EnAccess/OpenSmartMeter/hardware/design_images/3D PCB back.png

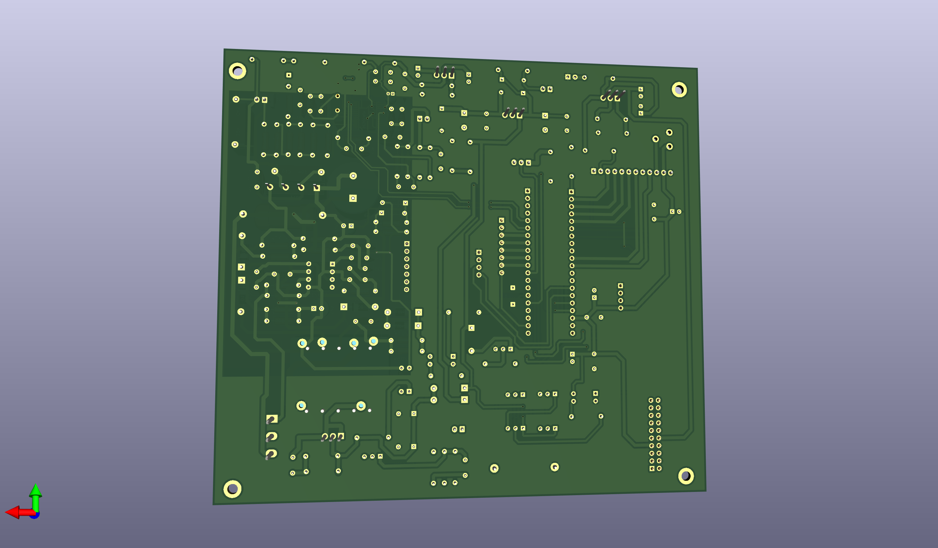
hardware/design_images/3D PCB back.png
