EnAccess/OpenSmartMeter/hardware/design_images/3D PCB front.png

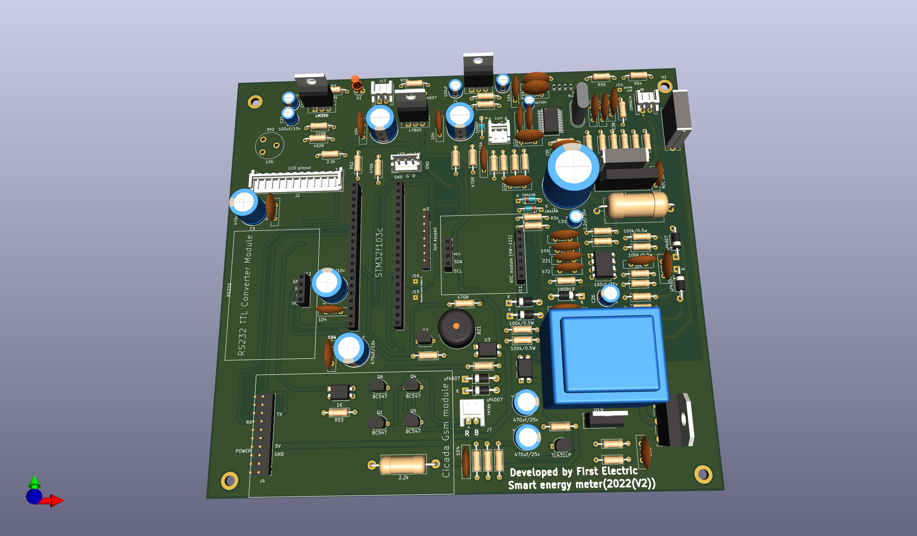
hardware/design_images/3D PCB front.png
