EnAccess/OpenSmartMeter/hardware/design_images/3D PCB right side view.png

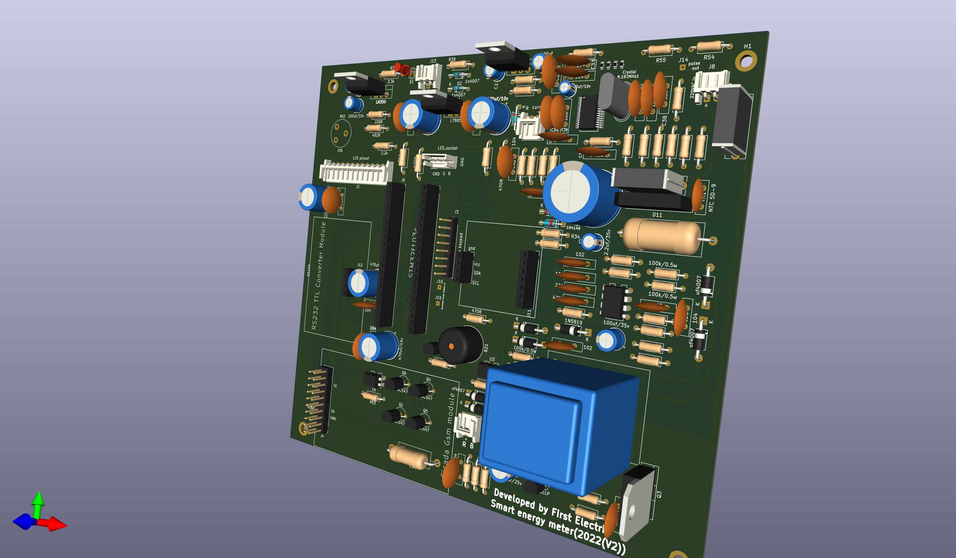
hardware/design_images/3D PCB right side view.png
