EnAccess/OpenSmartMeter/hardware/design_images/first meter prototype.JPG

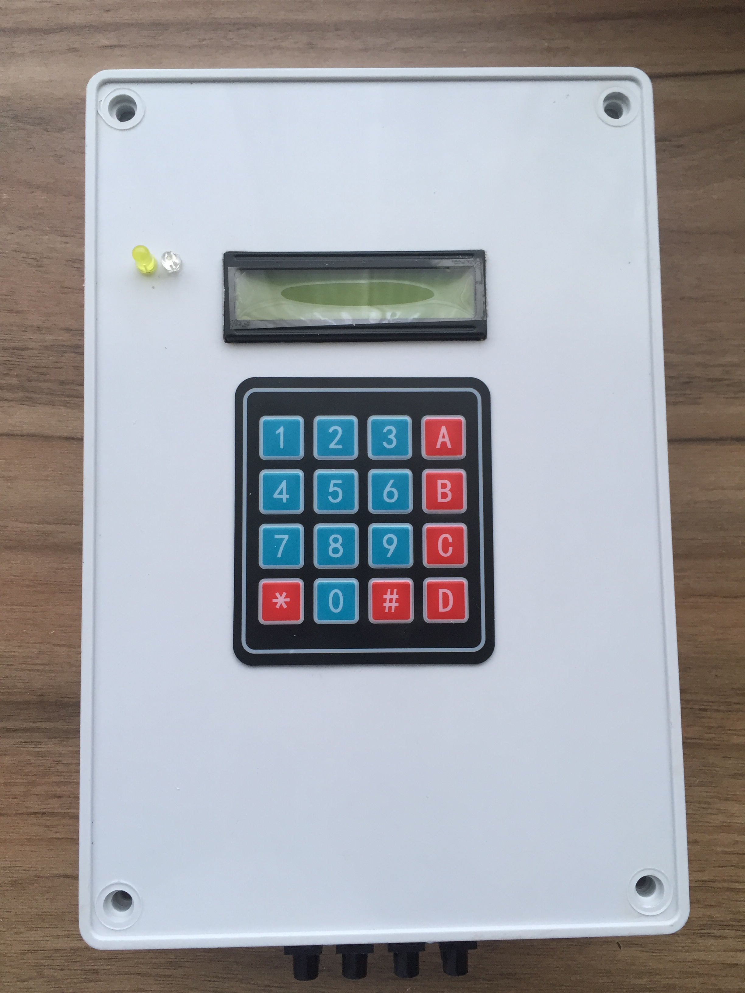
hardware/design_images/first meter prototype.JPG
