EnAccess/OpenSmartMeter/hardware/design_images/meter25 terminal block view.JPG

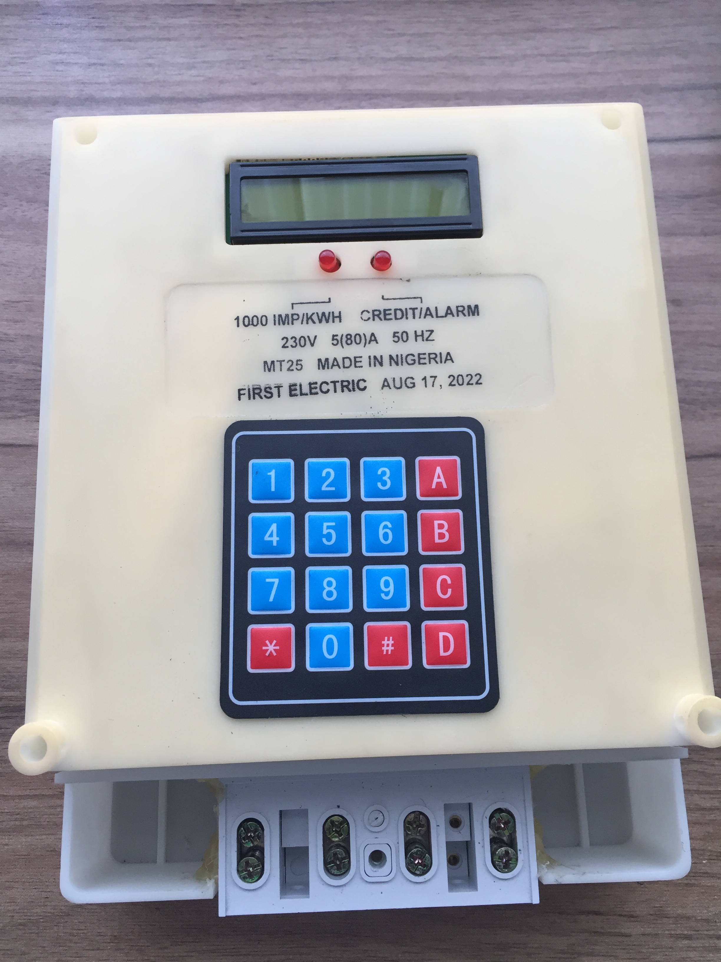
hardware/design_images/meter25 terminal block view.JPG
