EnAccess/OpenSmartMeter/hardware/design_images/meter50 terminal block view.JPG

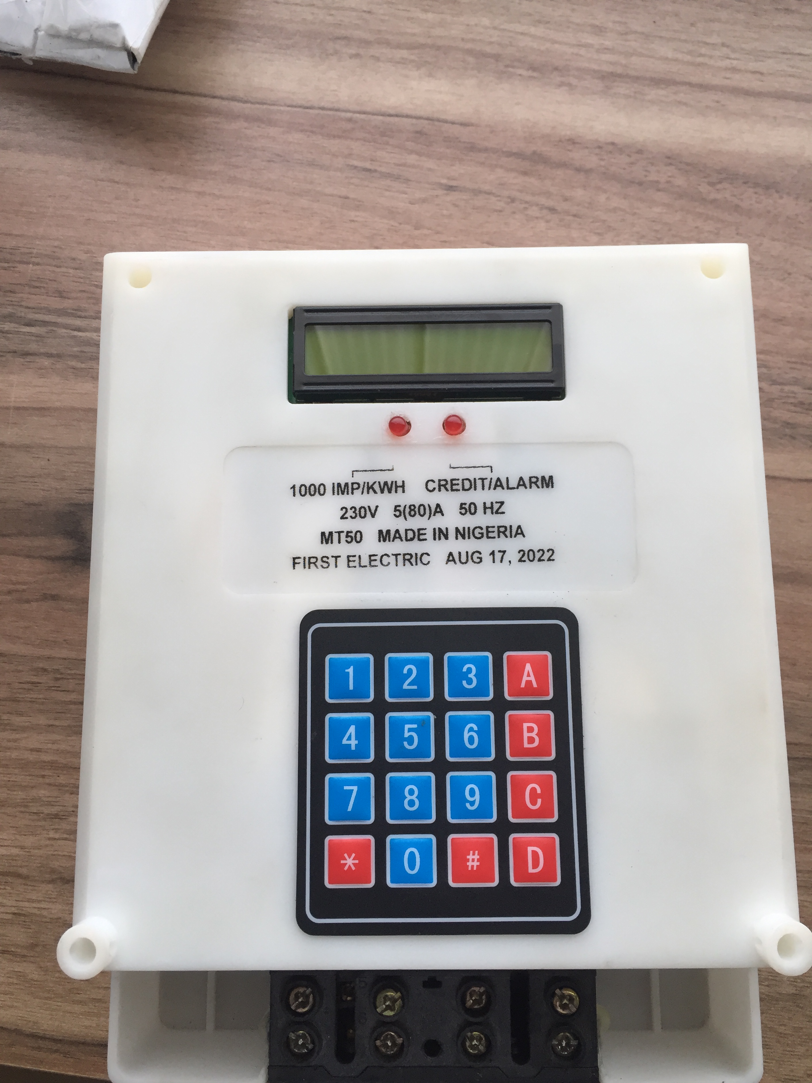
hardware/design_images/meter50 terminal block view.JPG
