EnAccess/OpenSmartMeter/hardware/design_images/meter100.JPG

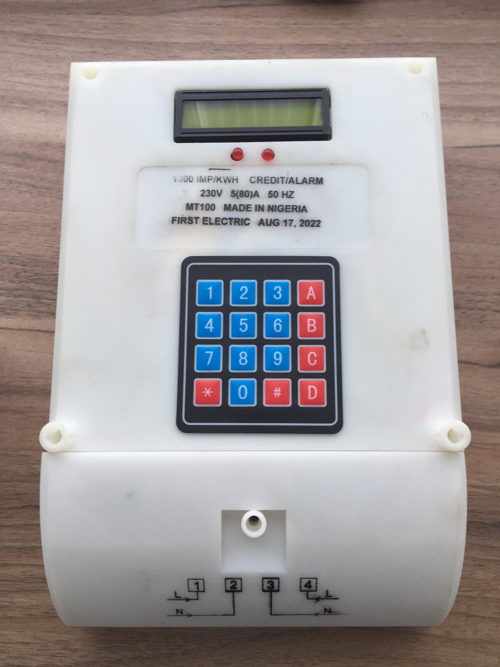
hardware/design_images/meter100.JPG
