EnAccess/OpenSmartMeter/hardware/exterior_casing_design/meter bottom view.png

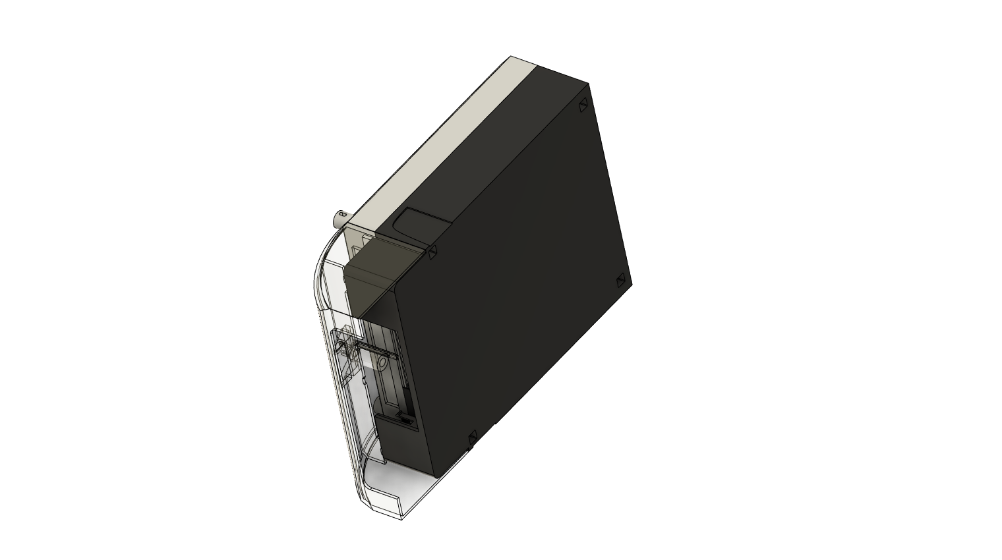
hardware/exterior_casing_design/meter bottom view.png
