EnAccess/OpenSmartMeter/web_software/assets/img/abt.jpg

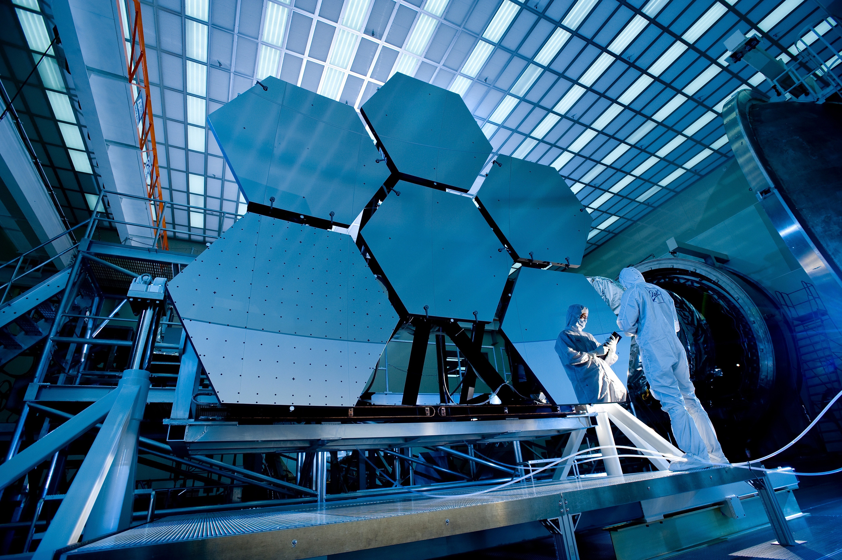
web_software/assets/img/abt.jpg
