EnAccess/OpenSmartMeter/web_software/assets/img/hero-bg-3.jpg

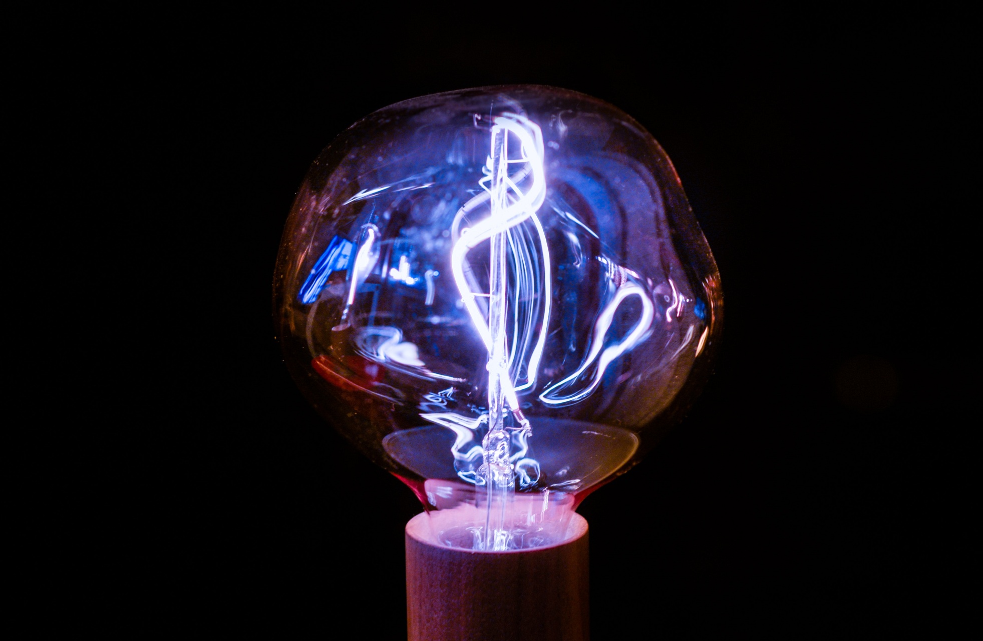
web_software/assets/img/hero-bg-3.jpg
