EnAccess/OpenSmartMeter/web_software/assets/img/hero-bg.jpg

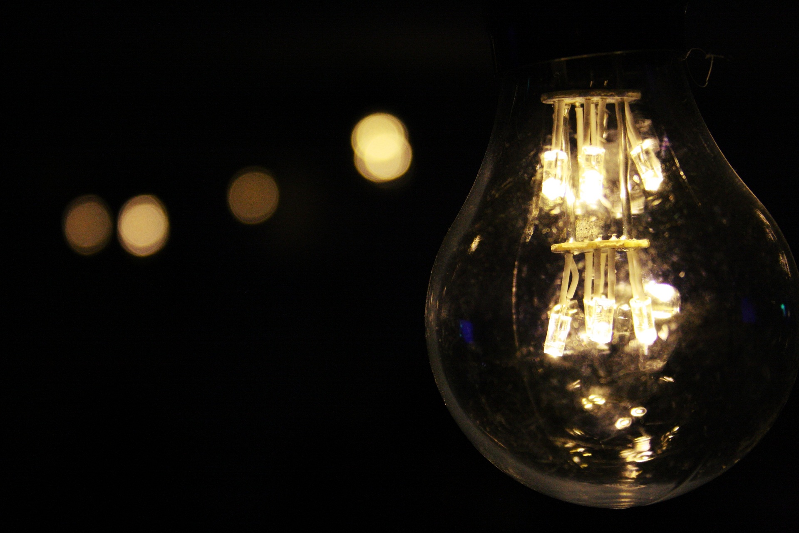
web_software/assets/img/hero-bg.jpg
