EnAccess/OpenSmartMeter/web_software/img/background.jpg

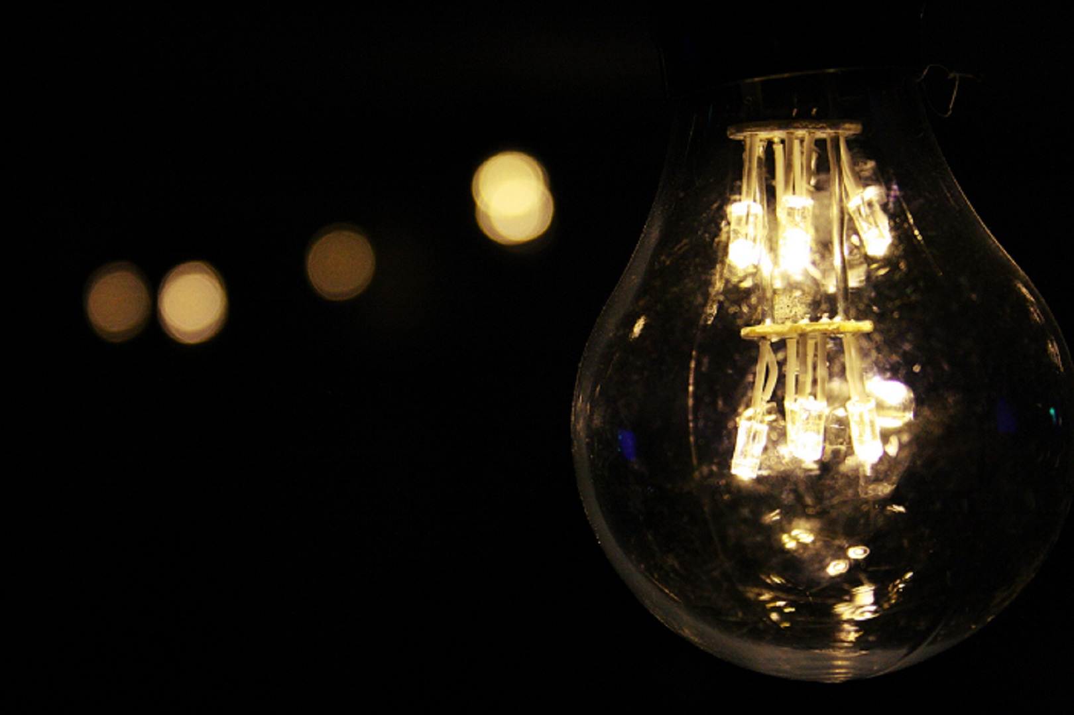
web_software/img/background.jpg
