EnAccess/OpenSmartMeter/web_software/img/sts1.jpg

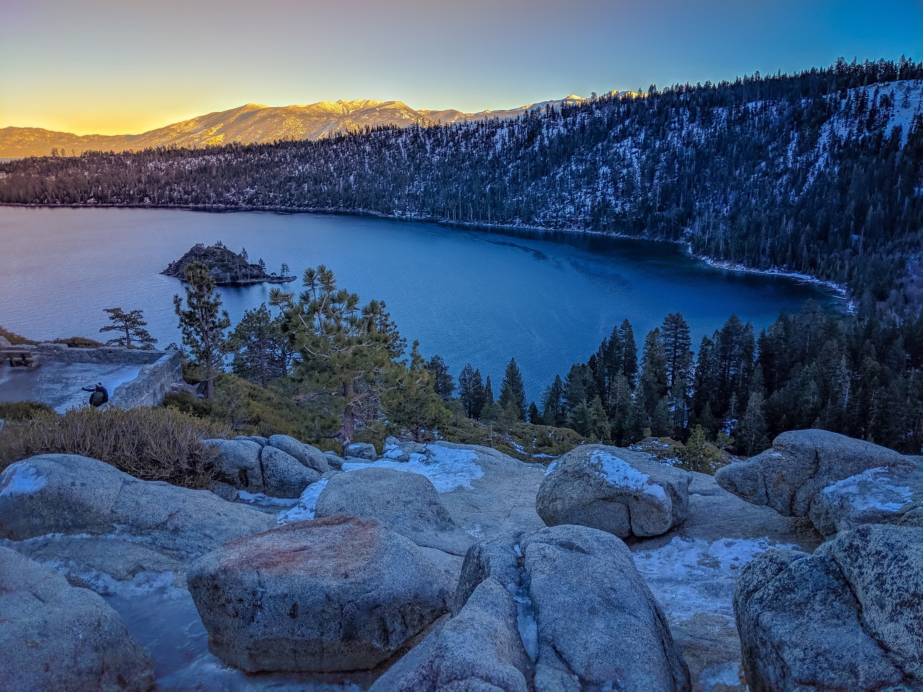
web_software/img/sts1.jpg
