EnAccess/OpenSmartMeter/web_software/img/sts2.jpg

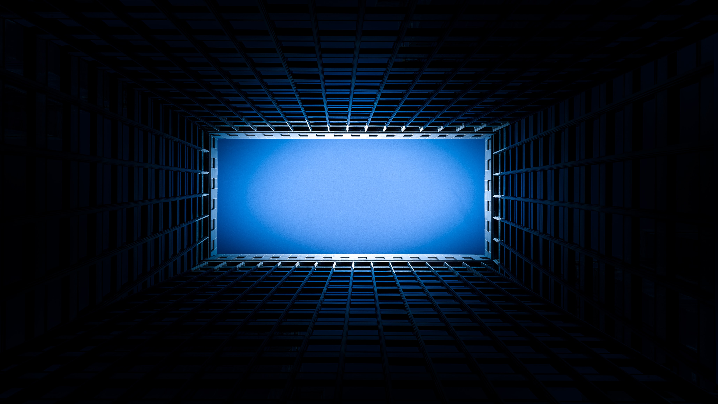
web_software/img/sts2.jpg
