EnAccess/OpenSmartMeter/hardware/design_images/preassembled meter.JPG

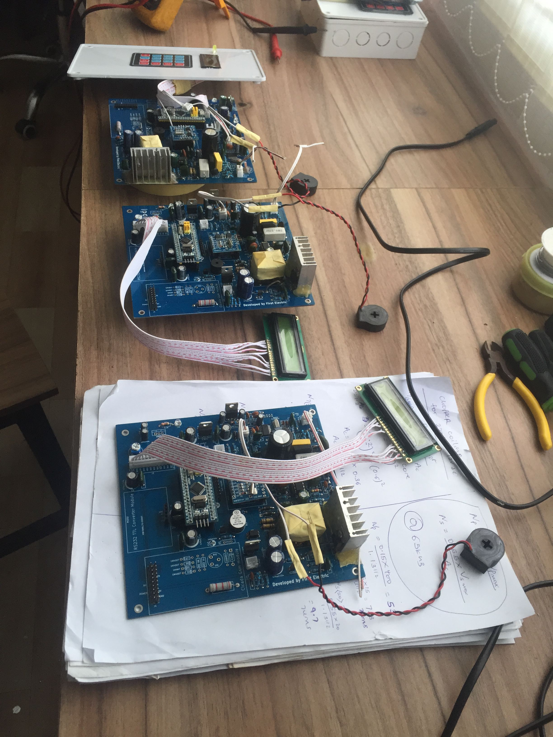
hardware/design_images/preassembled meter.JPG
