EnAccess/OpenSmartMeter/hardware/design_images/soldered PCB2.JPG

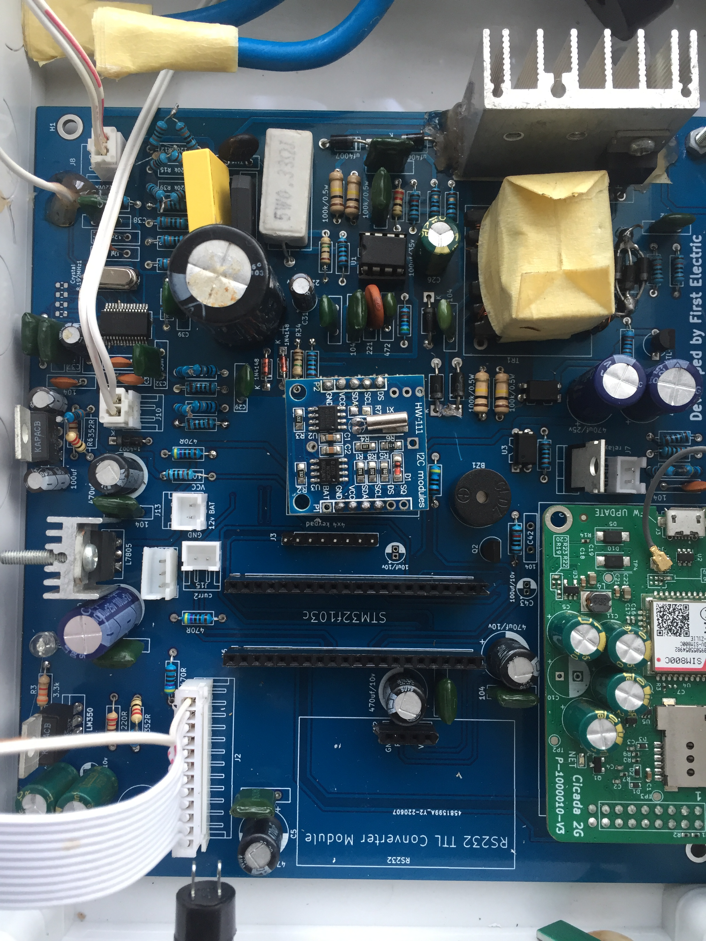
hardware/design_images/soldered PCB2.JPG
