EnAccess/OpenSmartMeter/hardware/design_images/soldered PCB.JPG

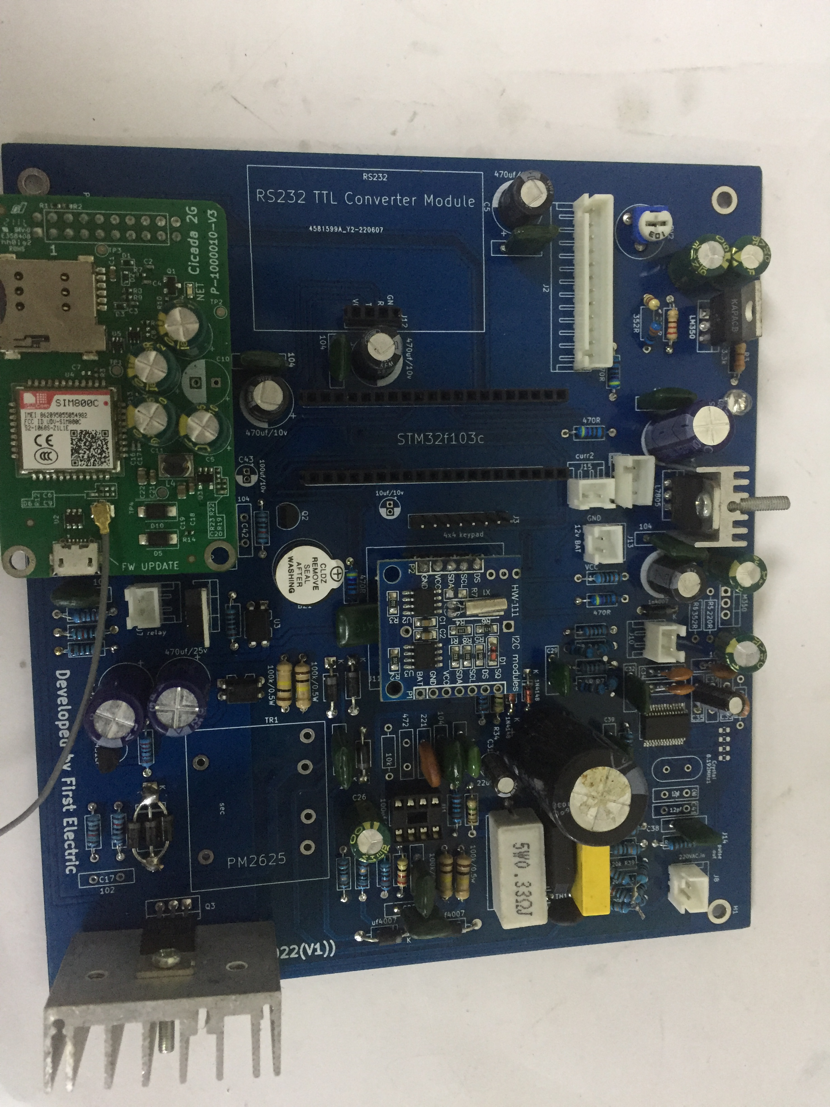
hardware/design_images/soldered PCB.JPG
